MillerLabFTW/Perfusion/Luer tip calibration/Tip STLs/0.3.stl

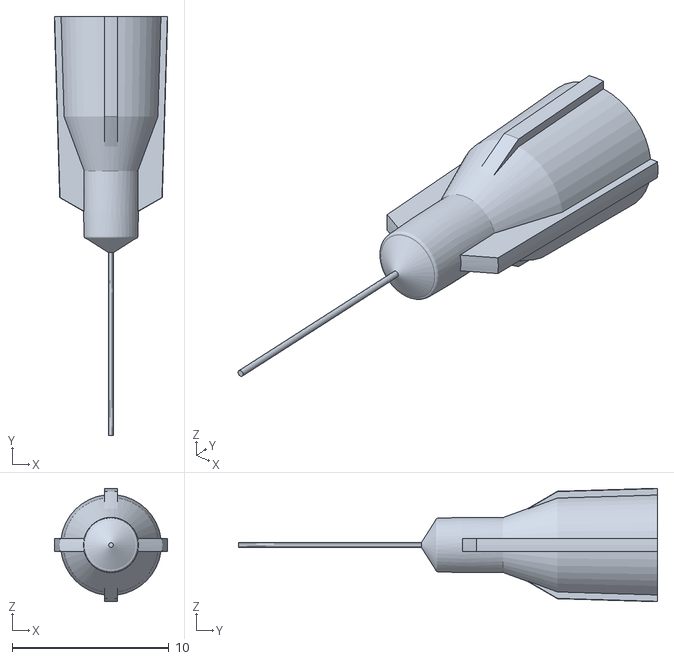
[picture p31: CAD file, 2021-05-25]
Luer tip calibration/Tip STLs/0.3.stl
7.23 x 26.7 x 7.23
