MillerLabFTW/Perfusion/Perfusion accessories/VerticalPerfusionStand.stl

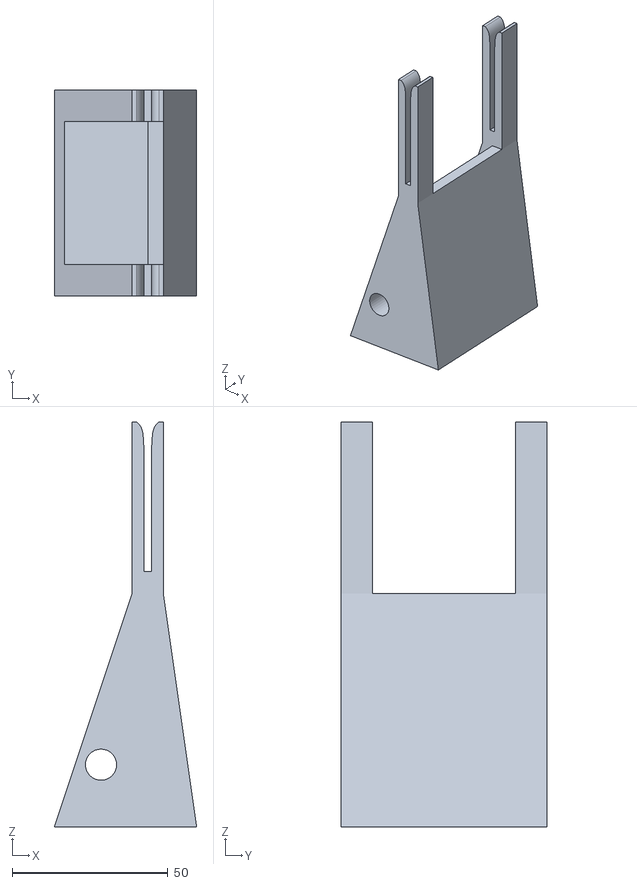
[picture p32: CAD file, 2020-04-16]
Perfusion accessories/VerticalPerfusionStand.stl
45.7 x 66.0 x 130.0
