MillerLabFTW/Perfusion/Perfusion chamber generator/Example chamber STL files/Demo_Chamber_OpenBottom+PDMSAnchors.stl

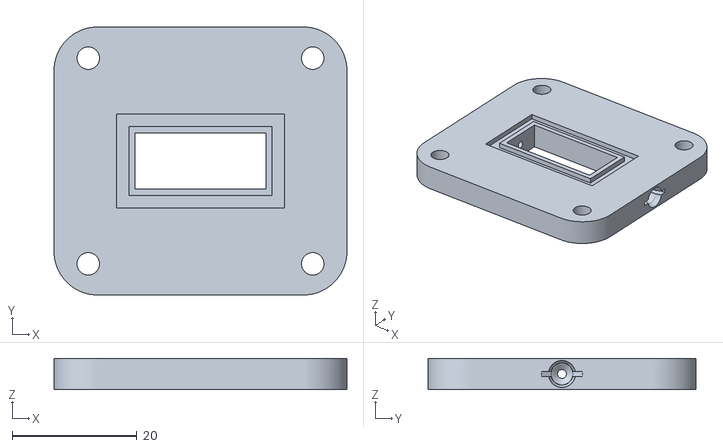
[picture p33: CAD file, 2020-04-16]
Perfusion chamber generator/Example chamber STL files/Demo_Chamber_OpenBottom+PDMSAnchors.stl
47.0 x 43.0 x 5.00
