MillerLabFTW/Perfusion/Perfusion accessories/OffsetChamberStand.SLDPRT

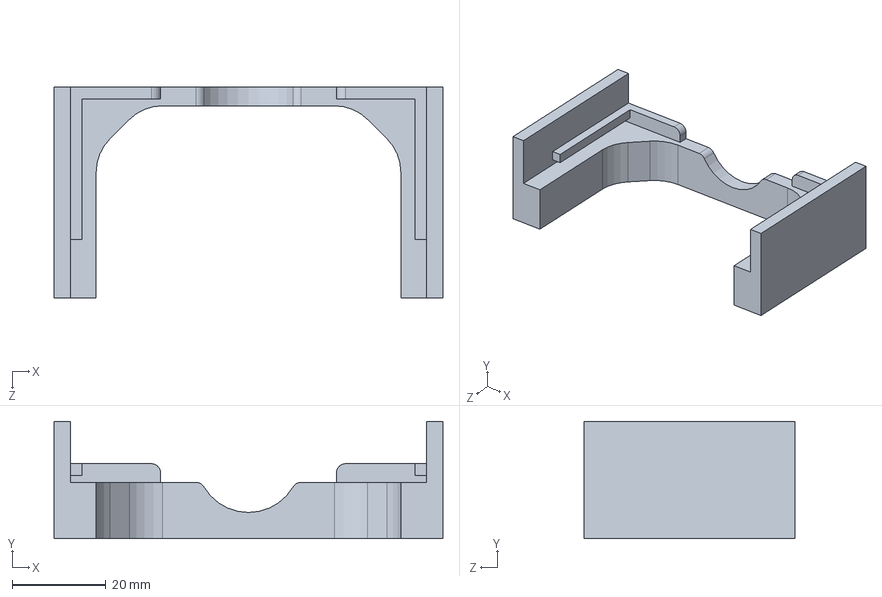
[picture p35: CAD file, 2020-04-16]
Perfusion accessories/OffsetChamberStand.SLDPRT
83.0 x 25.0 x 45.0 mm
