MillerLabFTW/Perfusion/Perfusion chamber generator/Example chamber STL files/Demo_Chamber_ExtraPorts.stl

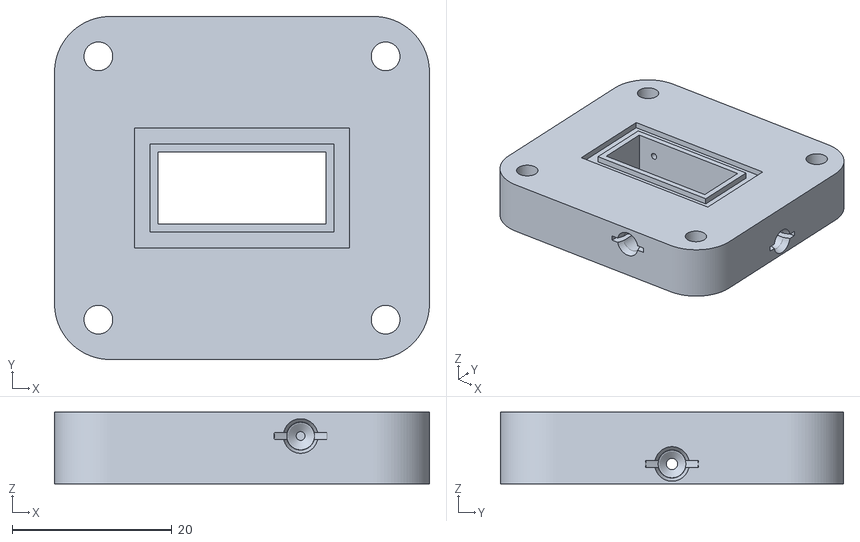
[picture p36: CAD file, 2020-04-16]
Perfusion chamber generator/Example chamber STL files/Demo_Chamber_ExtraPorts.stl
47.0 x 43.0 x 9.00
