MillerLabFTW/Perfusion/Perfusion accessories/ExtrusionRack_mount_hanging_version.stl

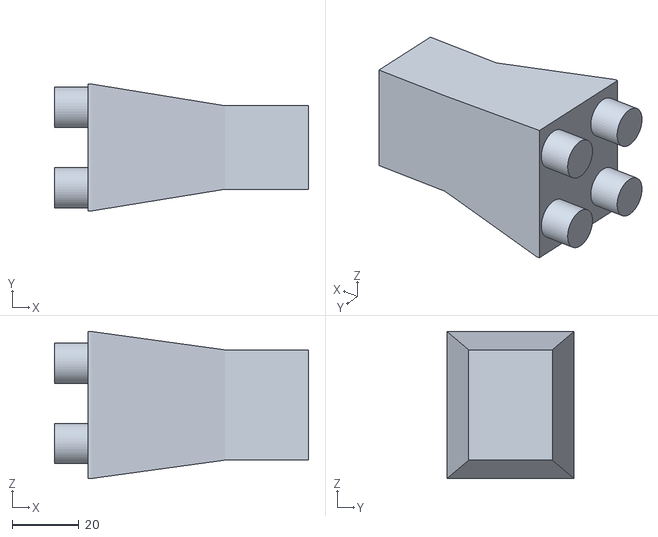
[picture p37: CAD file, 2020-04-16]
Perfusion accessories/ExtrusionRack_mount_hanging_version.stl
76.0 x 38.0 x 44.0
