MillerLabFTW/Perfusion/Perfusion chamber generator/Example chamber STL files/Demo_Chamber_SolidBottom+NeedleGasket.stl

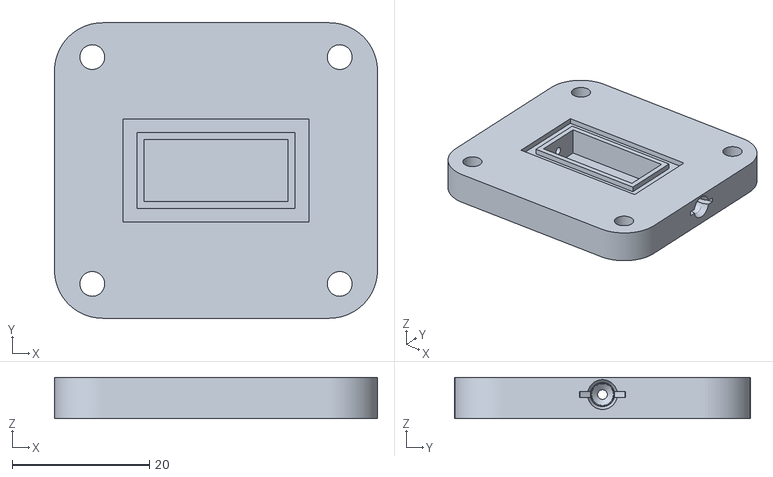
[picture p38: CAD file, 2020-04-16]
Perfusion chamber generator/Example chamber STL files/Demo_Chamber_SolidBottom+NeedleGasket.stl
47.0 x 43.0 x 6.00
