MillerLabFTW/Perfusion/Luer tip calibration/Tip STLs/2.0.stl

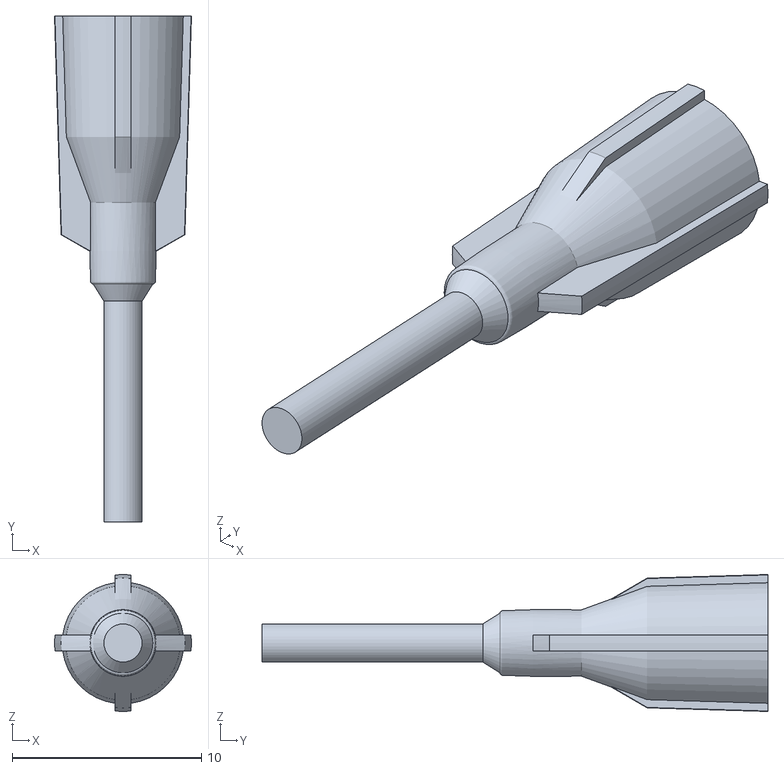
[picture p41: CAD file, 2021-05-25]
Luer tip calibration/Tip STLs/2.0.stl
7.23 x 26.7 x 7.23
